joefscholtz/current_monitoring_esp32/components/network_manager/src/wifi_handler.c

#include "esp_log.h"
#include "esp_wifi.h"

static const char *TAG = "WIFI_H";

esp_err_t wifi_handler_init(void) {
  esp_netif_create_default_wifi_sta();
  wifi_init_config_t cfg = WIFI_INIT_CONFIG_DEFAULT();
  ESP_ERROR_CHECK(esp_wifi_init(&cfg));

  wifi_config_t wifi_config = {
      .sta =
          {
              .ssid = CONFIG_WIFI_SSID,
              .password = CONFIG_WIFI_PASSWORD,
          },
  };

  ESP_ERROR_CHECK(esp_wifi_set_mode(WIFI_MODE_STA));
  ESP_ERROR_CHECK(esp_wifi_set_config(WIFI_IF_STA, &wifi_config));
  ESP_ERROR_CHECK(esp_wifi_start());
  ESP_ERROR_CHECK(esp_wifi_connect());

  ESP_LOGI(TAG, "Wi-Fi Station initialized.");
  return ESP_OK;
}
